maheen055/Skittle-Sorter/gear_cap.stl

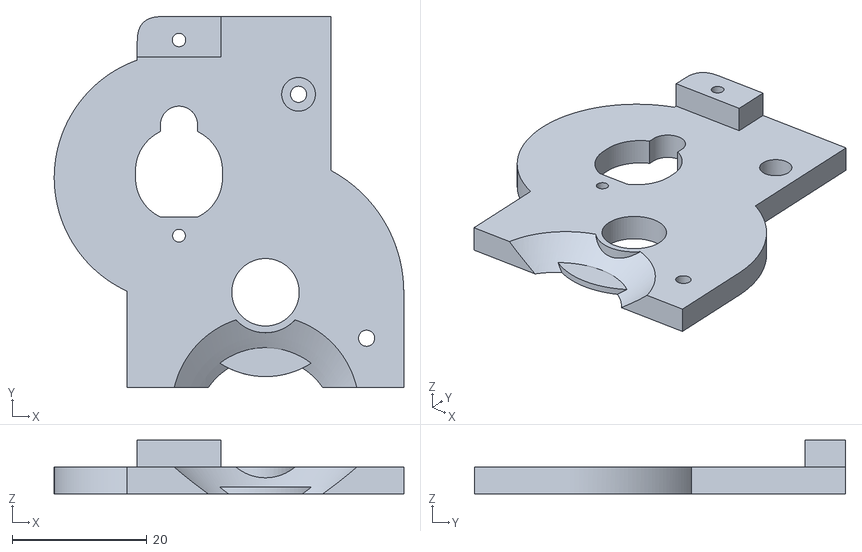
[picture p15: CAD file, 2025-03-18]
gear_cap.stl
51.8 x 55.0 x 8.00
